RadioThermal/RadioThermal_Soldering_OSHW/Cable/media/IMG_5341.jpeg

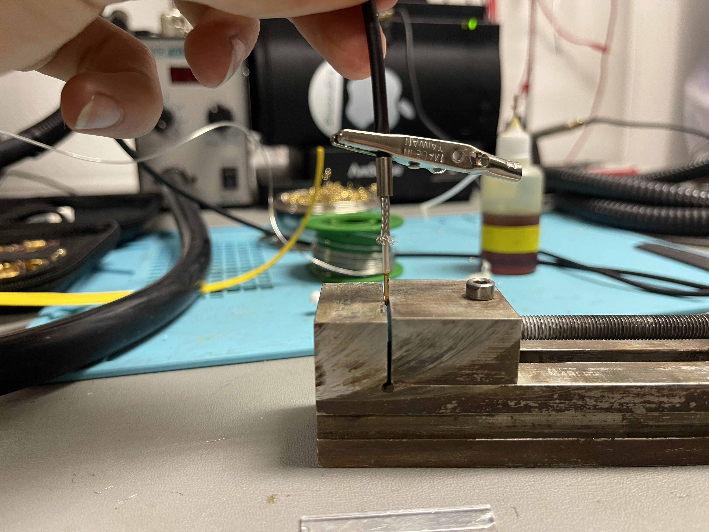
Cable/media/IMG_5341.jpeg
