RadioThermal/RadioThermal_Soldering_OSHW/Cable/media/IMG_5344.jpeg

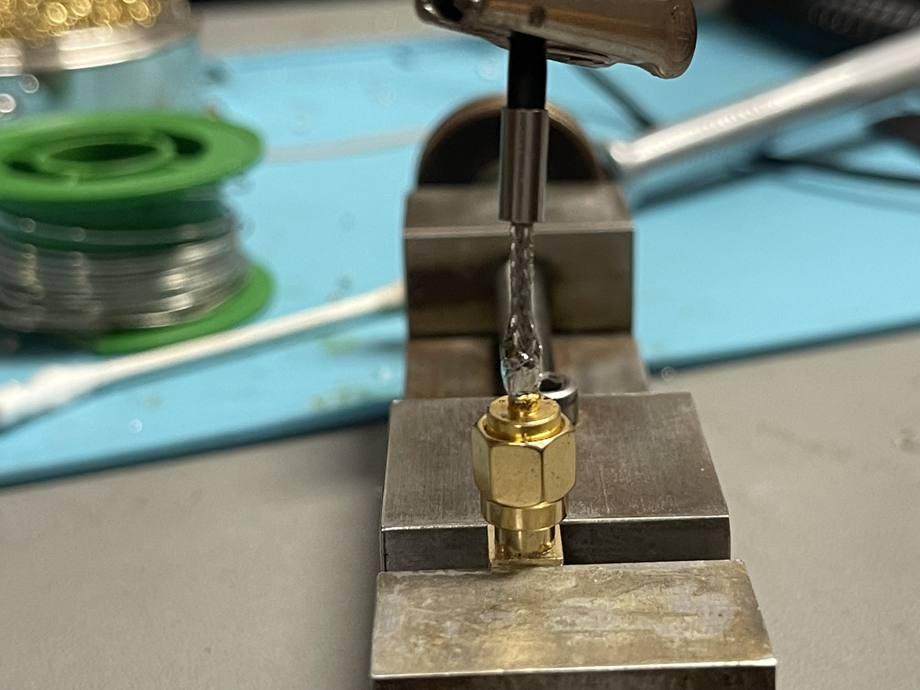
Cable/media/IMG_5344.jpeg
