RadioThermal/RadioThermal_Soldering_OSHW/Power Supply/media/PCB2_3B.jpg

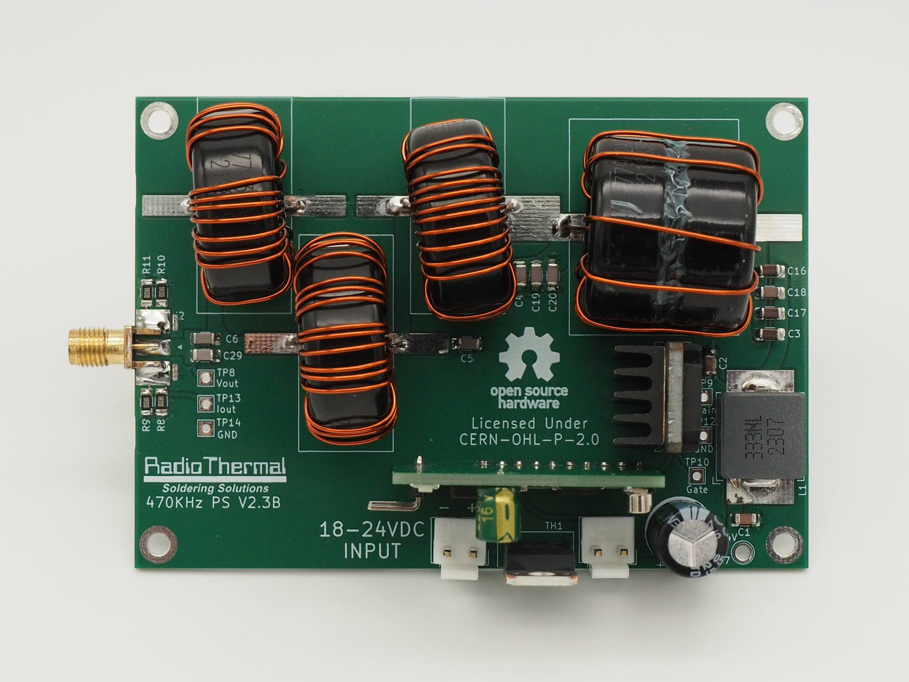
Power Supply/media/PCB2_3B.jpg
