RadioThermal/RadioThermal_Soldering_OSHW/Handpiece/media/All-Parts.jpg

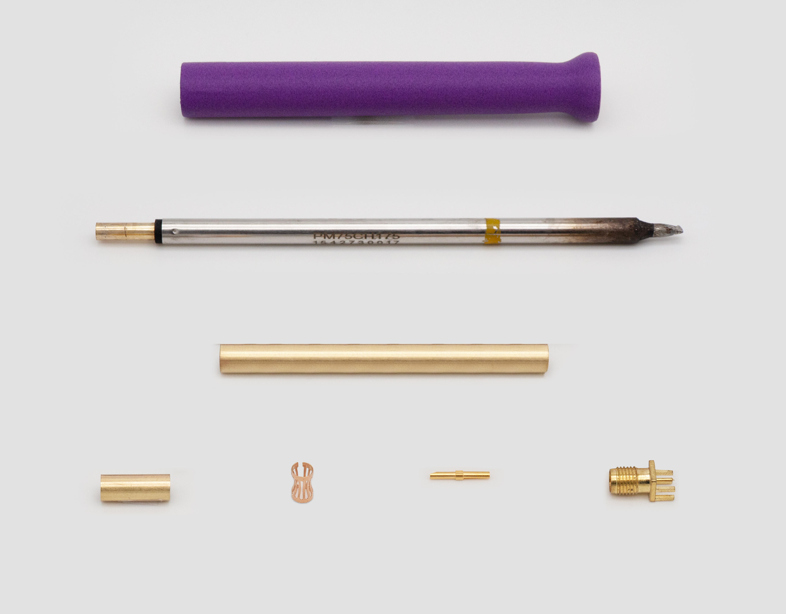
Handpiece/media/All-Parts.jpg
