RadioThermal/RadioThermal_Soldering_OSHW/Power Supply/PCB/KiCad files/Custom_3D_models/TO-220-3_Vertical_heatsink.step

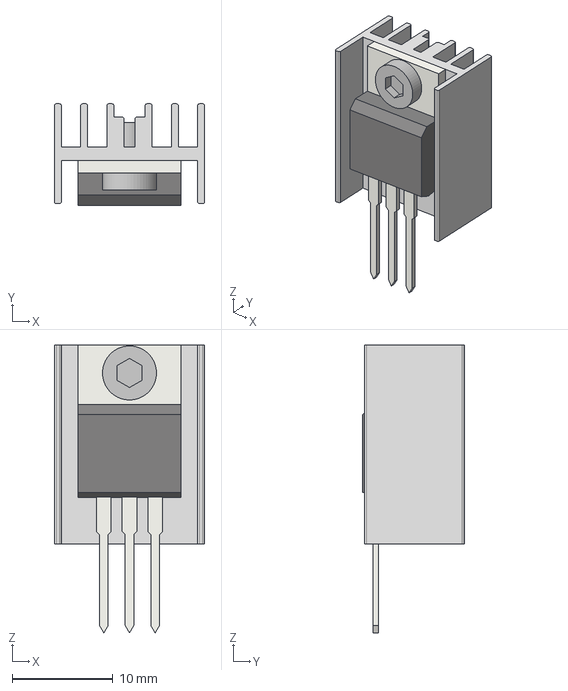
[picture p37: CAD file, 2026-09-04]
Power Supply/PCB/KiCad files/Custom_3D_models/TO-220-3_Vertical_heatsink.step
14.9 x 10.1 x 28.5 mm
