RadioThermal/RadioThermal_Soldering_OSHW/Power Supply/PCB/KiCad files/Custom_3D_models/B2P-VH-LF--SN---3DModel-STEP-510211.STEP

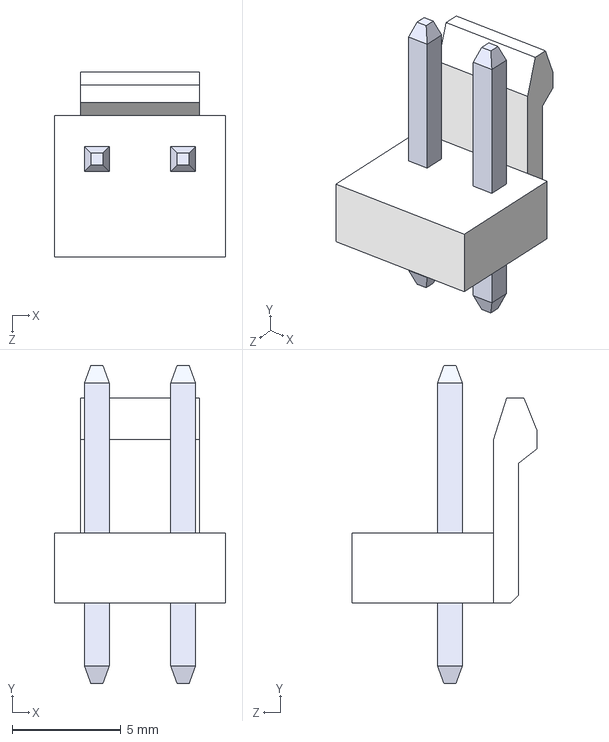
[picture p38: CAD file, 2026-09-04]
Power Supply/PCB/KiCad files/Custom_3D_models/B2P-VH-LF--SN---3DModel-STEP-510211.STEP
7.86 x 14.6 x 8.50 mm
