RadioThermal/RadioThermal_Soldering_OSHW/Power Supply/PCB/KiCad files/Custom_3D_models/33uh inductor.step

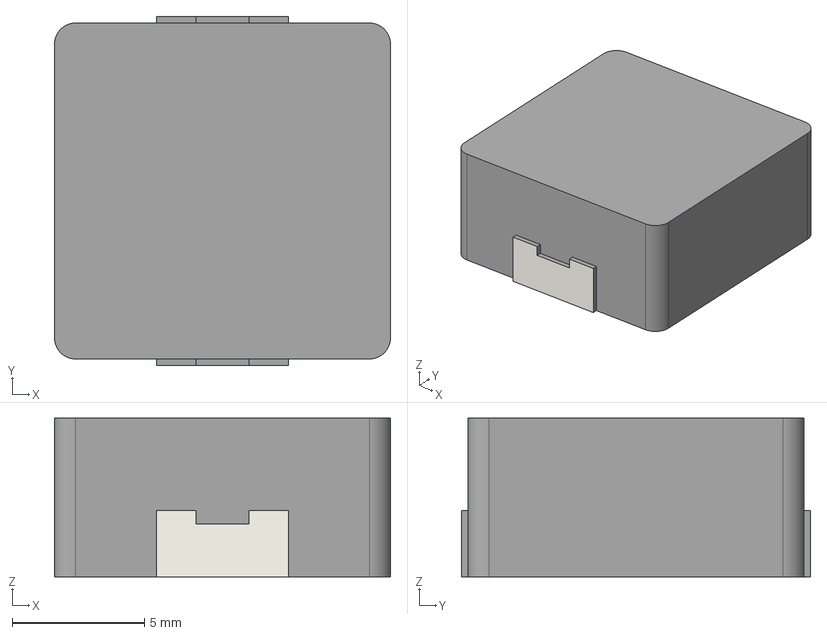
[picture p39: CAD file, 2026-09-04]
Power Supply/PCB/KiCad files/Custom_3D_models/33uh inductor.step
12.7 x 13.2 x 6.00 mm
