RadioThermal/RadioThermal_Soldering_OSHW/Power Supply/PCB/KiCad files/Custom_3D_models/RTSS_Power_Supply_V2-5B.step

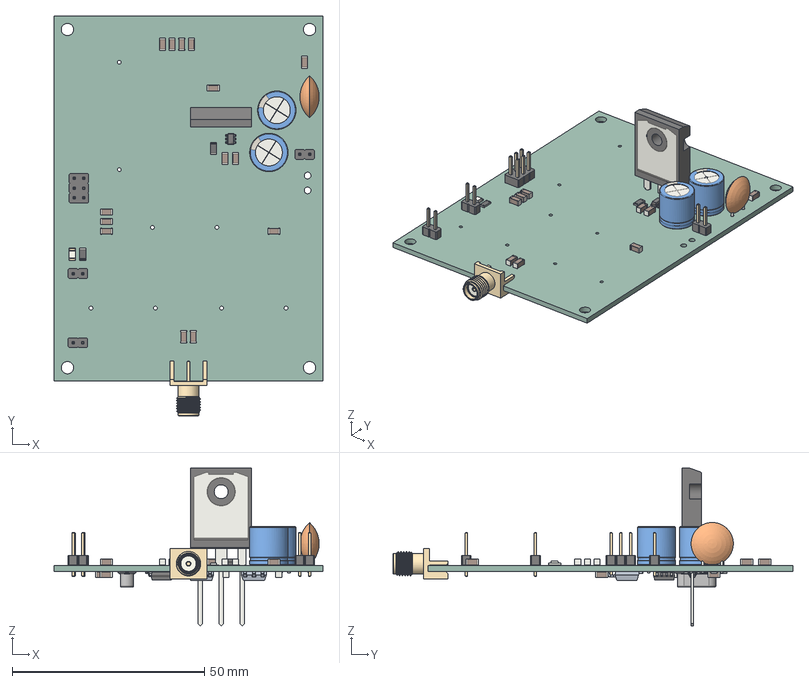
[picture p40: CAD file, 2026-03-16]
Power Supply/PCB/KiCad files/Custom_3D_models/RTSS_Power_Supply_V2-5B.step
70.0 x 104.1 x 41.1 mm
TO-247-3_Vertical
PinHeader_2x03_P2.54mm_Vertical
C_1206_3216Metric x 20
R_1206_3216Metric x 6
PinHeader_1x02_P2.54mm_Vertical x 3
CP_Radial_D10.0mm_P5.00mm_P7.50mm x 2
LED_1206_3216Metric
SOT-23-6
SMA_Molex_73251-1153_EdgeMount_Horizontal
C_Disc_D11.0mm_W5.0mm_P5.00mm
pcbv2 1.28.1 x 2
Crystal_SMD_HC49-SD
SOIC-8_5.3x5.3mm_P1.27mm
SOT-23-5
pcbv2_PCB
